Modurail/walk-through/2016 Walk-through Wiring.sch

## KiCad design 2016 Walk-through Wiring.sch (2016-03-03)

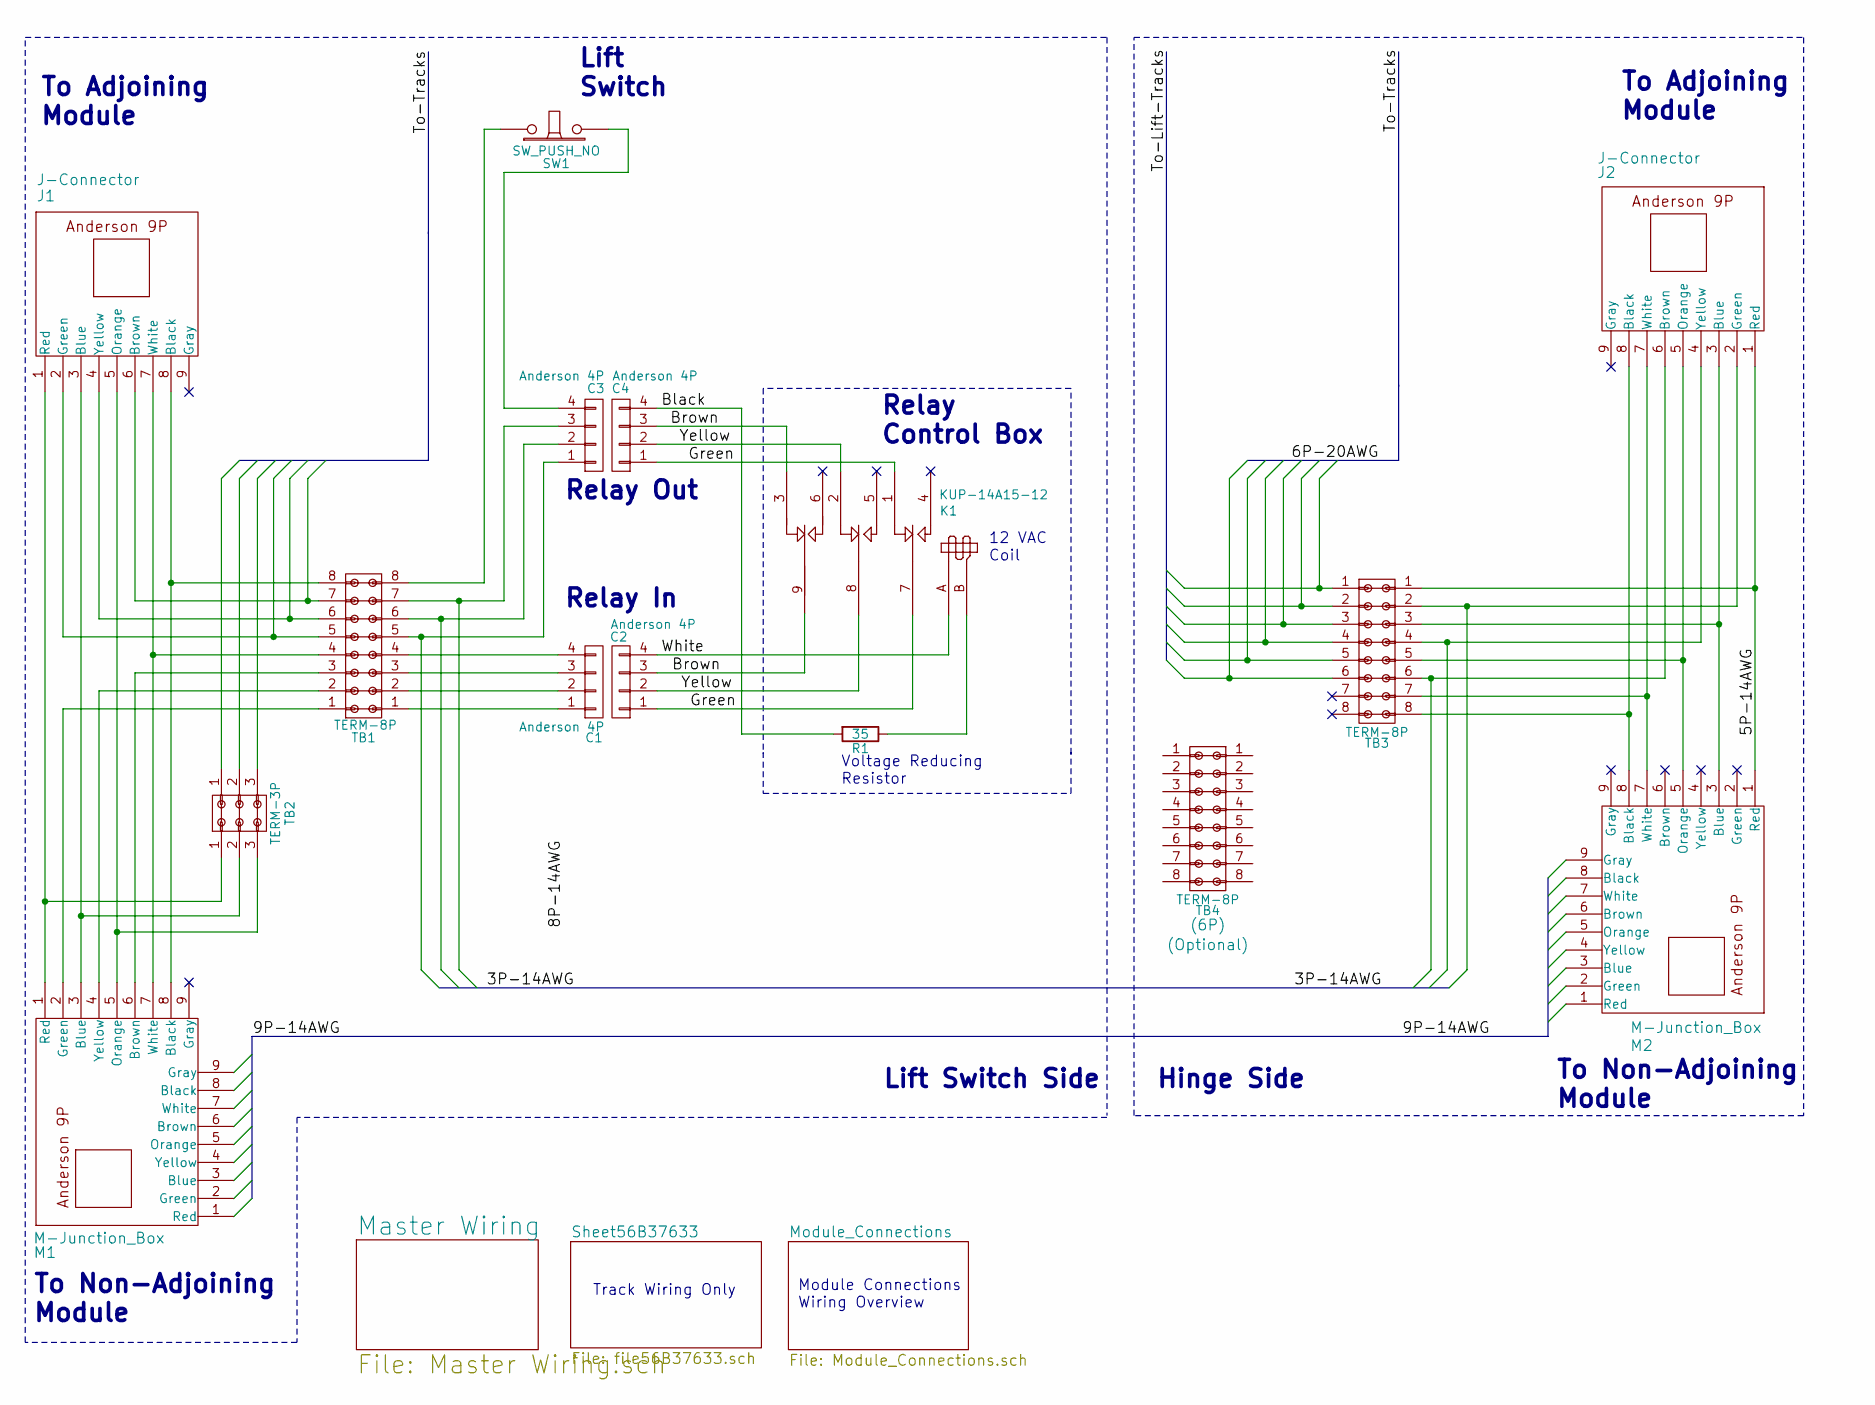
[picture p9: schematic 2016 Walk-through Wiring.sch]

Parts:
C1, C2, C3, C4: Anderson 4P
J1, J2: J-Connector
K1: KUP-14A15-12
M1, M2: M-Junction_Box
R1: 35
SW1: SW_PUSH_NO
TB1, TB3, TB4: TERM-8P
TB2: TERM-3P

Connections:
5P-14AWG: J2.1 (Red), M2.1 (Red), TB3.1
Black: C4.4, R1.2
Brown: C2.3, C4.3, K1.3 (R3), K1.9 (C3)
Green: C2.1, C4.1, K1.1 (R1), K1.7 (C1)
unnamed: C1.1, TB1.1
unnamed: C1.2, TB1.2
unnamed: C1.3, TB1.3
unnamed: C1.4, TB1.4
unnamed: C3.1, TB1.5
unnamed: C3.2, TB1.6
unnamed: C3.3, TB1.7
unnamed: C3.4, SW1.2
unnamed: J1.1 (Red), M1.1 (Red), TB2.1
unnamed: J1.2 (Green), TB1.5
unnamed: J1.3 (Blue), M1.3 (Blue), TB2.2
unnamed: J1.4 (Yellow), TB1.6
unnamed: J1.5 (Orange), M1.5 (Orange), TB2.3
unnamed: J1.6 (Brown), TB1.7
unnamed: J1.7 (White), M1.7 (White), TB1.4
unnamed: J1.8 (Black), M1.8 (Black), TB1.8
unnamed: J2.2 (Green), TB3.2
unnamed: J2.3 (Blue), M2.3 (Blue), TB3.3
unnamed: J2.4 (Yellow), TB3.4
unnamed: J2.5 (Orange), M2.5 (Orange), TB3.5
unnamed: J2.6 (Brown), TB3.6
unnamed: J2.7 (White), M2.7 (White), TB3.7
unnamed: J2.8 (Black), M2.8 (Black), TB3.8
unnamed: K1.B, R1.1
unnamed: M1.2 (Green), TB1.1
unnamed: M1.4 (Yellow), TB1.2
unnamed: M1.6 (Brown), TB1.3
unnamed: SW1.1, TB1.8
White: C2.4, K1.A
Yellow: C2.2, C4.2, K1.2 (R2), K1.8 (C2)

Notes on the sheet:
12 VAC Coil
Relay Control Box
To Adjoining Module
To Non-Adjoining Module
Lift Switch
Relay In
Relay Out
Voltage Reducing Resistor
Track Wiring Only
Hinge Side
Lift Switch Side
Module Connections Wiring Overview
