Modurail/walk-through/file56B37633.sch

## KiCad design file56B37633.sch (2016-03-03)

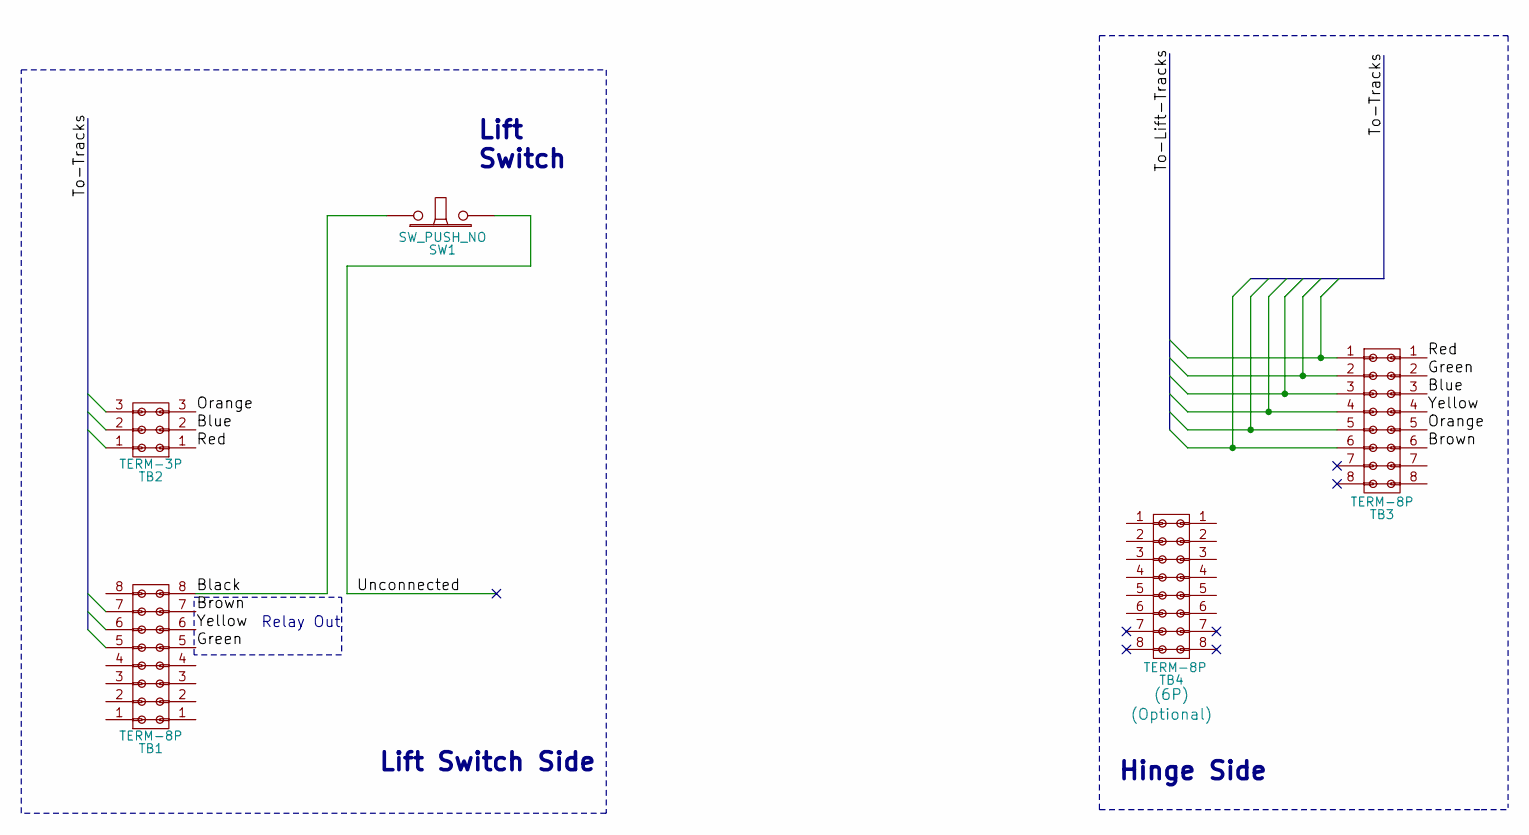
[picture p10: schematic file56B37633.sch]

Parts:
SW1: SW_PUSH_NO
TB1, TB3, TB4: TERM-8P
TB2: TERM-3P

Connections:
Black: SW1.1, TB1.8
Blue: TB2.2, TB3.3
Brown: TB1.7, TB3.6
Green: TB1.5, TB3.2
Orange: TB2.3, TB3.5
Red: TB2.1, TB3.1
Unconnected: SW1.2
Yellow: TB1.6, TB3.4

Notes on the sheet:
Hinge Side
Lift Switch Side
Lift Switch
Relay Out
